Stan6314/TinyBasRV/src/TinyBas/User/ch32v00x_conf.h

/********************************** (C) COPYRIGHT *******************************
 * File Name          : ch32v00x_conf.h
 * Author             : WCH
 * Version            : V1.0.0
 * Date               : 2020/08/08
 * Description        : Library configuration file.
*********************************************************************************
* Copyright (c) 2021 Nanjing Qinheng Microelectronics Co., Ltd.
* Attention: This software (modified or not) and binary are used for 
* microcontroller manufactured by Nanjing Qinheng Microelectronics.
*******************************************************************************/
#ifndef __CH32V00x_CONF_H
#define __CH32V00x_CONF_H

#include <ch32v00x_adc.h>
//#include <ch32v00x_dbgmcu.h>
//#include <ch32v00x_dma.h>
#include <ch32v00x_exti.h>
#include <ch32v00x_flash.h>
#include <ch32v00x_gpio.h>
#include <ch32v00x_i2c.h>
#include <ch32v00x_it.h>
#include <ch32v00x_iwdg.h>
#include <ch32v00x_misc.h>
#include <ch32v00x_pwr.h>
#include <ch32v00x_rcc.h>
#include <ch32v00x_spi.h>
#include <ch32v00x_tim.h>
#include <ch32v00x_usart.h>
#include <ch32v00x_wwdg.h>
#include <ch32v00x_opa.h>



#endif /* __CH32V00x_CONF_H */


	
	
	
